IlanSchindler/The-Pickle-Project/Final Cart Sheets (PDF and PNG)/Bari Sax Cart.png

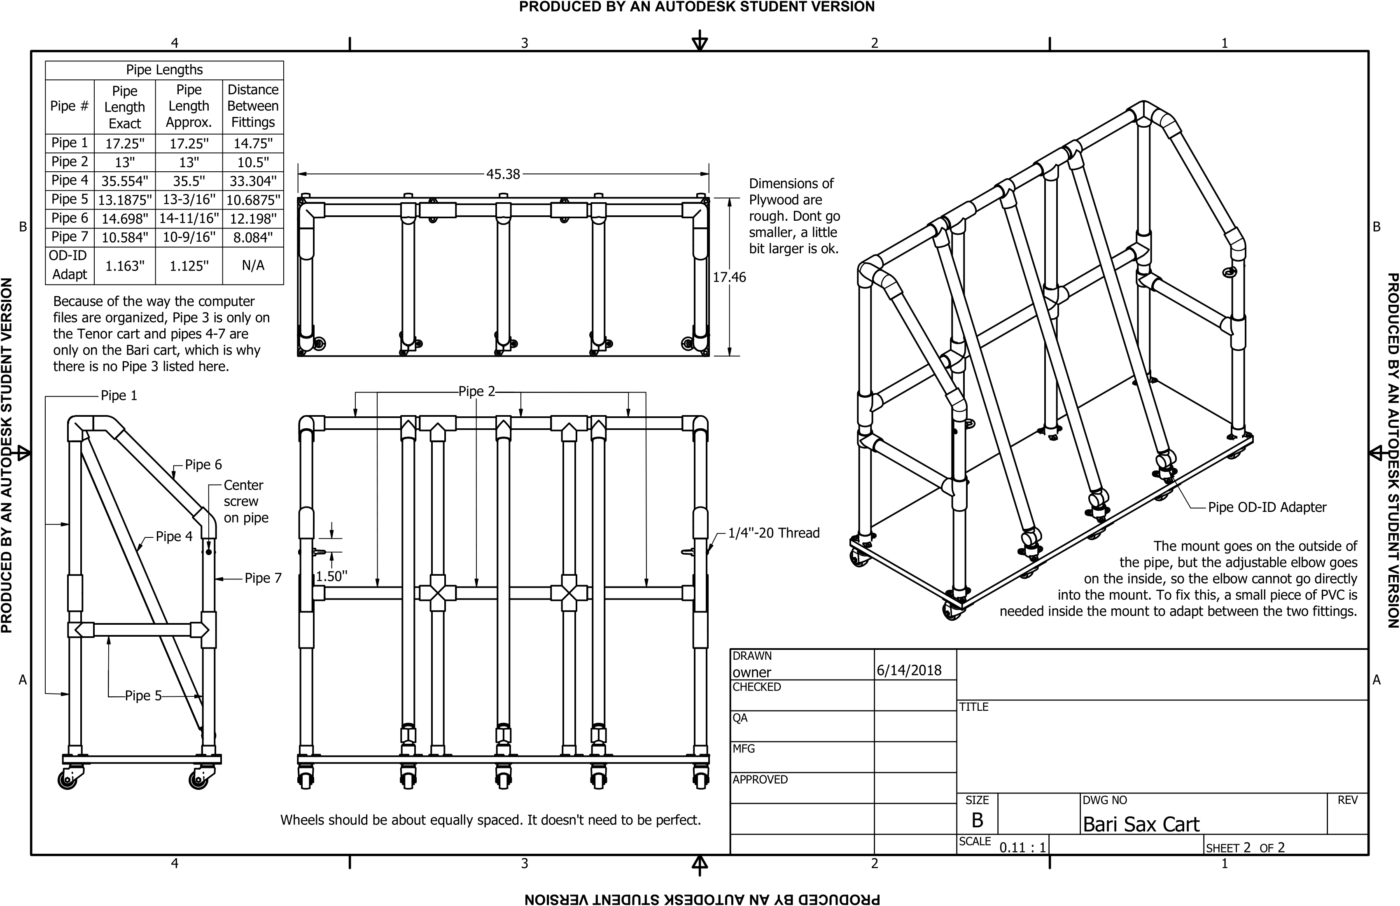
Final Cart Sheets (PDF and PNG)/Bari Sax Cart.png
