IlanSchindler/The-Pickle-Project/Final Cart Sheets (PDF and PNG)/Pickle Interior Modifications.png

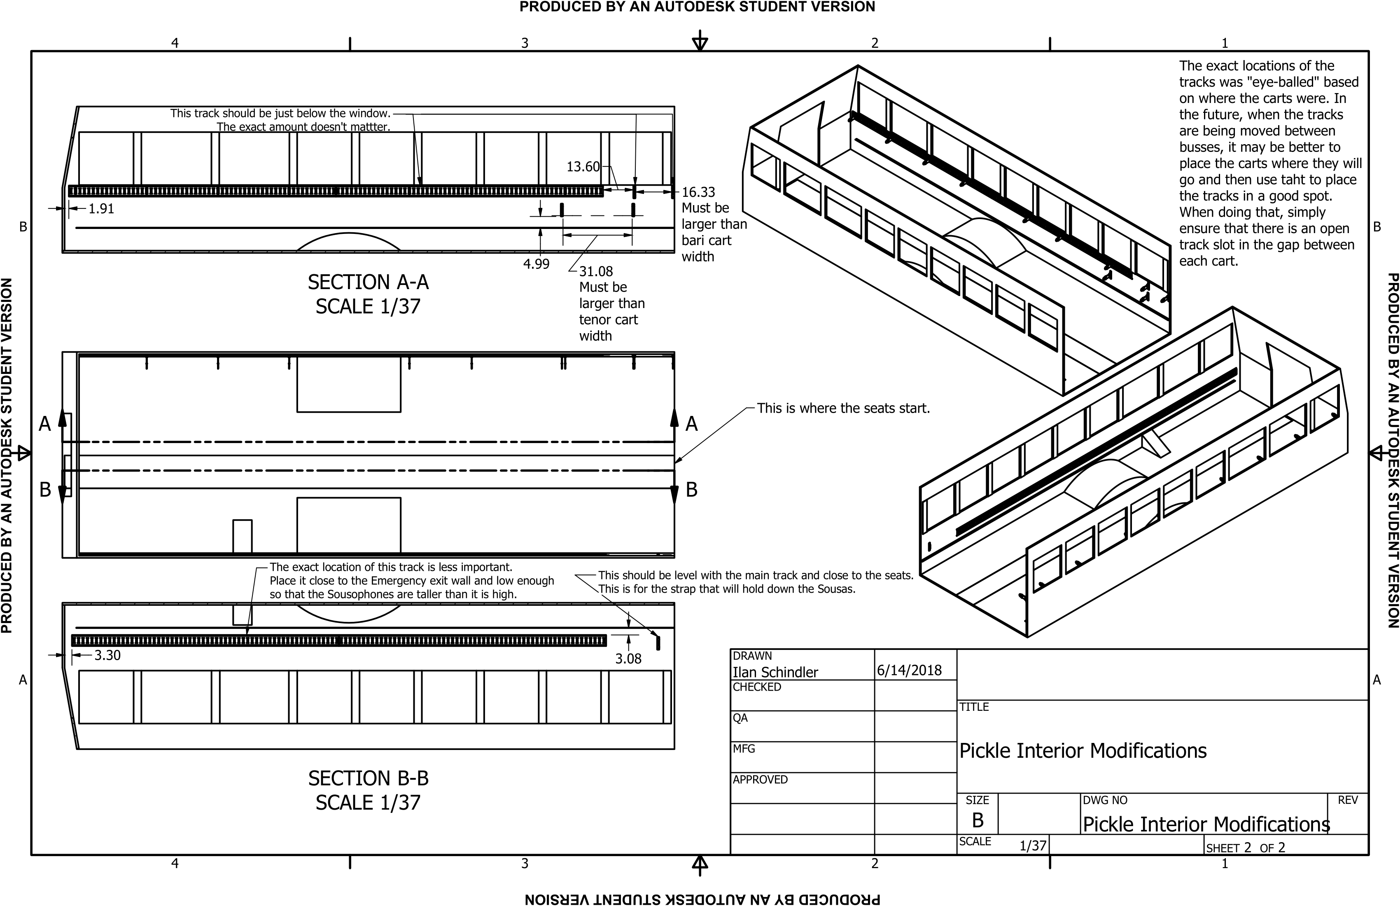
Final Cart Sheets (PDF and PNG)/Pickle Interior Modifications.png
