IlanSchindler/The-Pickle-Project/Final Cart Sheets (PDF and PNG)/T-Bone Cart.png

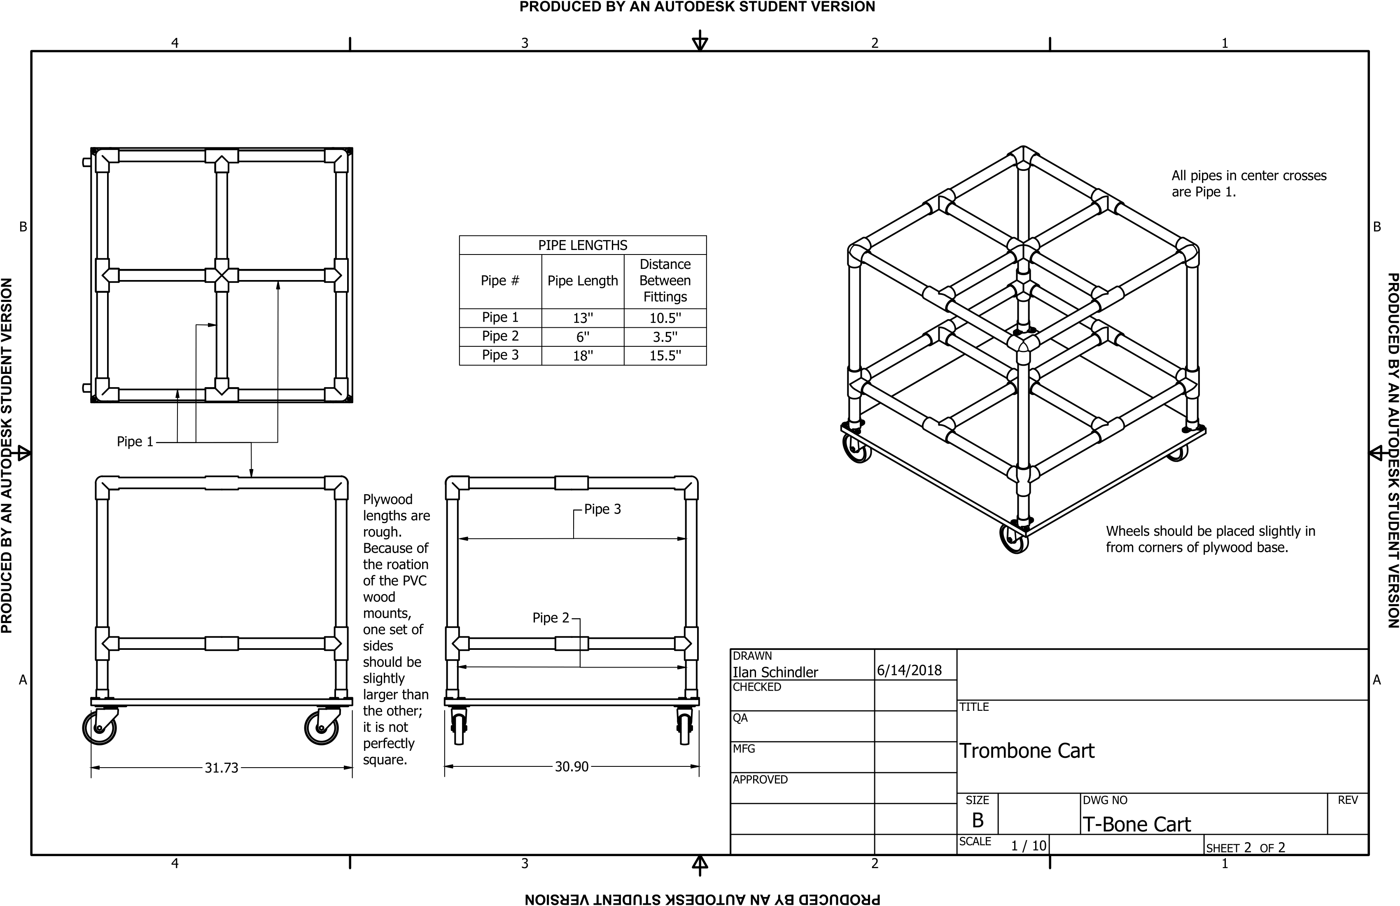
Final Cart Sheets (PDF and PNG)/T-Bone Cart.png
